hairykiwi/OTM-02/pcb/OTM-02.sch

## KiCad design pcb/OTM-02.sch (2013-09-27)

Schematic: OTM-02.sch

Parts:
C1, C2, C8, C14, C19, C32, C33, C34: 10N
C3, C6, C9, C10, C13, C20, C23, C24, C25, C27: 100N
C4, C5: 9P
C7, C12: 10P
C11, C17: 10U; PartNo_1 C1608X5R0J106M
C15, C21: 1U
C16: 1U; Voltage 10VDC
C18, C22, C31: 4U7; Voltage 10VDC
C26, C28, C29, C30: 2U2
D1: PZU3.3B1
D2, D3, D5: 1PS79SB30
D4: IP4221CZ6-S
J1: USB_MICRO_AB
J2: FH19SC-10S-0.5SH(05)
J3: ACHLR-02V-S
L1: WE-742792641
L2: WE-742792662
LED1: ASMT-CW00
M1: 304-103
P1: DBG_VCC
P2: DBG_SWDIO
P3: DBG_GND
P4: DBG_SWCLK
P5: DBG_SWO
P6: DBG_RESETn
Q1: FK6K02010L; WSMini6-F1-B
Q2: MTM761110LBF; WSMini6-F1-B
Q3: PDTC114EE
R1, R2, R8, R9, R11, R14, R16, R17: 100K
R3: 500R
R4, R10: 10K
R5: 1R
R6, R7: 15R
R12, R13: 4K7
R15: 10R
SP1, SP2: 0910-1-57-20-75-14-11-0
SW1, SW2, SW3, SW4, SW5: KMS221GPLFS
U1: EFM32LG330F256
U2: ADXL362
U3: MCP73831T-2ACI/MC
U4, U5: TPS78230DRVT
U6: MAX17048G+
X1: ABS06-32.768KHZ-9-1-T
X2: ABM11-48.000MHZ-B7G-T
X3: 7BB-20-3

Notes on the sheet:
Fit one of the following Sharp Microelectronics Memory LCDs: LS013B4DN02 - 96x96 1.35" LS013B7DH03 - 128x128 1.26" LS013B7DH01 - 144x168 1.28" or similar. Details here: sharpmemorylcd.com
NOTE: The above switch circuits require software debounce to be implemented.
Battery: Li-Po 3.7V 150mAh P/N: CS-IPSF5SL 15*24*2.5mm
NOTES 2: X1 previously: 815-ABM8G-48-B4Y-T (Abracon, 3.3x2.6mm) Q2 Previously: IRLML2244TRPBF Piezo driving: http://hades.mech.northwestern.edu/index.php/Driving_a_piezo_speaker_with_a_PIC Consider adding UEXT - see Olimex.com. Maxim advice (AN5329): For all modes of power-up, be mindful of the nee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
• THIS IS A WORK IN PROGRESS, CONSIDER IT A STARTING POINT. • Latest version is available at: github.com/hairykiwi/OTM-02 • U1 Pin/function locations to be optimised according to PCB layout requirements. • All XX_PUSHER MCU inputs coincide with Low Energy Sense (LES) inputs for ease of implementing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
Special thanks to family, friends and colleagues who have put up with my (often ironic) obsession with watchmaking - in some cases for more than a decade.
"The time has come," the Walrus said..." (Lewis Carroll, 1872)
Backlight
X3 typically mounted in case-back and connected via SP1 & SP2 using spring-loaded contacts. P/N Details: 7BB-20-3: 20 mm dia, leadless 7BB-20-6L0: 20 mm dia, with 32AWG x 50 mm flying leads.
MCU AVDD isolation (Ferrite bead + 1R0): BLM21BD102S (2125/0805) - suggested in EM's AN0002 - Hardware Design Considerations Z=1000, R = 0R4, 0.3A - 2.0x 1.25 x0.85mm BK2125HS102-T (2125/0805) - Taiyo Yuden 1000 / 0R4 / 0.3A - 2.0x 1.25 x0.85mm BLM15AX102SN1D (1005/0402) - Murata - 1000 / 0R49 / 0.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
MCP73831T calcs: USB_VBUS: VMax = 5.25 STAT VMax = (VDD - 1 to VDD - 0.4) = 4.85 STAT VMin = (0.4 - 1.0) = 0.4 BAT_CHG_STAT Max range = 2.425 - 0.25V BAT_CHG_STAT Min range = 1.875 - 0.5V
This work is licensed under the Creative Commons Attribution-ShareAlike 3.0 Unported License. To view a copy of this license, visit http://creativecommons.org/licenses/by-sa/3.0/. Send comments, feedback, suggestions to: Hamish Mead info at meadtimemachines dot co dot uk With thanks to Microchip, S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
UEXT Connector (Olimex Standard) For possible implementation Pin Name I/O Logic Primary Use 1 3.3V S S +3.3 volt 2 GND S S Ground 3 TXD O PP Transmit Data for Async Serial bus 4 RXD I PP Receive Data for Async Serial bus 5 SCL O OD Clock for I2C bus 6 SDA I/O OD Bidirectional Serial Data for I2C bu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
CREDITS -------- Sparkfun: http://www.sparkfun.com/products/10617 and http://www.sparkfun.com/products/10711 Mark Burton - SmartAvionics.com Olimex.com Leucos - Piezo Precisionmicrodrives.com - EMC/EMI Best Practise examples WE-Online (UK) PCB support: Paul, Chris and team. + Others.
3V0 / 3V3 VDD Compatibility List ---------------------- RV3029: 1.3 - 5.5V (RTC) TPS78230DRV: 0 - 6V 3V REG EFM32LG330F256: 1.85 - 3.8V (MCU) 910-101: 3V Nom. - 1.6 - 3.6V (MOTOR) 310-103: 3V Nom. - 1.0 - 3.6V (MOTOR) 310-118: 3V Nom. - 1.2 - 3.3V (MOTOR) MCP73831T-2ACI/OT - N/A (LiPoCharger)
NOTES 1: 1. MTM-OTM-01: After initially implementing the 1724 step-up converter circuit, testing revealed the MLCD (LS01384DN02) appears to operate equally well from a 3V3 supply. 2. SCS, SI, SCLK, DISP: 3 V Amplitude | (IF UTILISED) EXTCOMIN: 5 V Amplitude 3. Regarding LS013B4DN02 VCOM: a. If a so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
304-103 (Permanent Magnet Motor): Perf Characteristics: For Vdd = 3.0V, I = 73 mA PWM Calcs: L = 600uH For C = 100nF - F(r) = 20.5kHz For C = 100pF - F(r) = 650kHz NOTE: If M1 substituted with brushless motor, PWM is NOT permitted.
NOTE: Microchip User Guide DS51729a shows 2U2* caps in place of the 4U7 recommended in the device datasheet. *2.2 μF 10V X5R 0603
Piezoelectric Diaphragm
Display - Sharp Microelectronics Memory LCD
USB Battery Charger and VMCU Regulator
LiPo Fuel Gauge
- For reference designs, recommendations and app notes see: http://bit.ly/Mey1VI and http://www.precisionmicrodrives.com/application-notes-technical-guides - Consider using X2Y 6R3X14W104MV4T for bypass filtering (Farnell code: 1886132) Details here: http://johansondielectrics.com/x2y-products.html
Vibratory Motor
(TO RESET MANUALLY, SHORT TO GND)
OPTIONAL: - USB_PU_EN Resistor ONLY required for LOW speed USB - USB_ID required only if host function implemented.
Low Frequency Clock
High Frequency Clock
USB MICRO AB Connection
R10 10K = approx. 100mA charge current 5K = approx. 200mA charge current
Debug Interface
Power Supply Decoupling
Pushers | Buttons (tact switches)
MEMORY LCD NOTES -------------------------- EXTMODE: When <H>, EXTCOMIN signal is enable. When <L> ,serial input flag is enable. C12 &C13 100N MINIMUM - May be 1U for convenience.
Major experimenting required with Hesaglas (0.3 - 0.5mm cast acrylic) + laser engraving to construct a planar lightguide as described by Idé et al.
CHANGES: Accelerometer added. Fuel Gauge IC updated to latest (smaller) model. Backlight LED now switched directly by MCU.
© Hamish Mead 2012-2013 - Licensed CC-BY-SA
Drive LED using <GPIO_Px_CTRL DRIVEMODE = STANDARD> + PWM. - Value of R to be confirmed. - Max current for ASMT-CW00 is 10mA. - VF varies from 2.55V (min) - 3.15V (max). - At 3V VMCU + Standard drive level, with draw of 10mA, GPIO voltage drops to approx 2.7V. As a result, LED should not be able to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
RES PINS - May be connected to ground or left unconnected. NC PINS - Not internally connected.
------------>> GENERAL NOTES ------------>>
Accelerometer
SP1 & SP2: MILL-MAX 0910-1 Spring-Loaded Pin - SMD Initial Height: 4.5 mm - Stroke: 1.4 mm Alternative: 0930 Spring-Loaded Pin - TH SOLDERTAIL Initial Height: 4.4 mm - Stroke: 1.4 mm
SP1 & SP2 P/N:
Replace ACHLR-02V-S: height:1.2 mm, with readily available ACHR-02V-S: height: 1.4 mm
